mayhem/hippie-trap/graphs/impulse.png

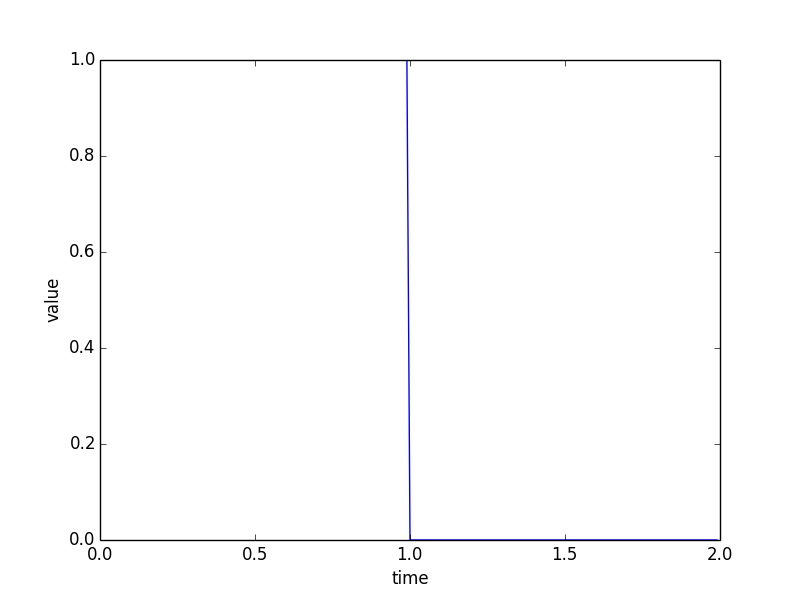
graphs/impulse.png
