mayhem/hippie-trap/graphs/sine.png

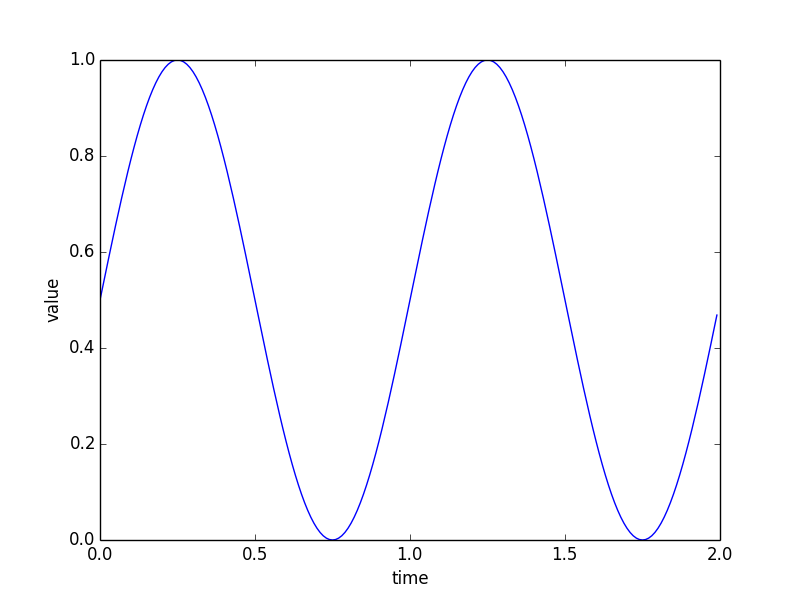
graphs/sine.png
