mayhem/hippie-trap/graphs/square.png

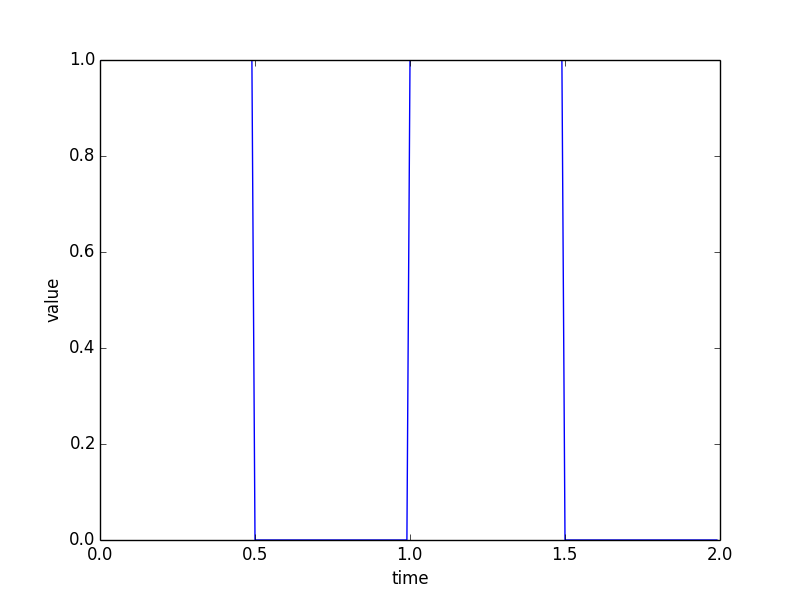
graphs/square.png
