mayhem/hippie-trap/graphs/step.png

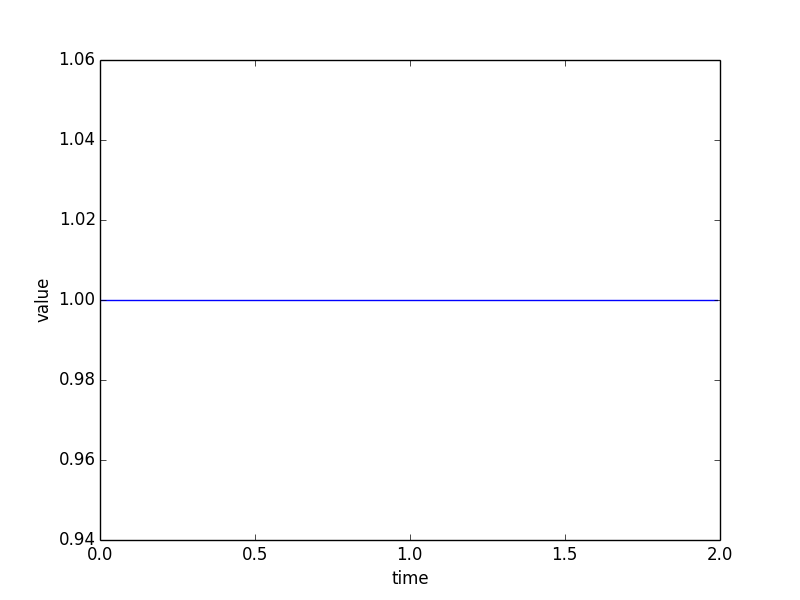
graphs/step.png
