mayhem/hippie-trap/firmware/node/colorspace.h

#ifndef COLORSPACE_H
#define COLORSPACE_H

#include "defs.h"

uint32_t clip_hue(uint32_t hue);
uint8_t hsv_to_rgb(int32_t h, int32_t s, int32_t v, color_t *color);
uint8_t hueshift_to_rgb(uint32_t hue_shift, int32_t h, int32_t s, int32_t v, color_t *color);
uint8_t rgb_to_hsv(color_t *col, int32_t *_h, int32_t *_s, int32_t *_v);

#endif
