mayhem/hippie-trap/firmware/node/function.h

#ifndef __FUNCTION_H__
#define __FUNCTION_H__

#include <stdio.h>
#include <math.h>
#include <math.h>
#include <stdint.h>
#include <stdlib.h>
#include "defs.h"

void apply_pattern(int32_t t, uint8_t *data, uint8_t len);

#endif
